DomiIRL/rgb-cube/models/tests/standoff_test_preview.png

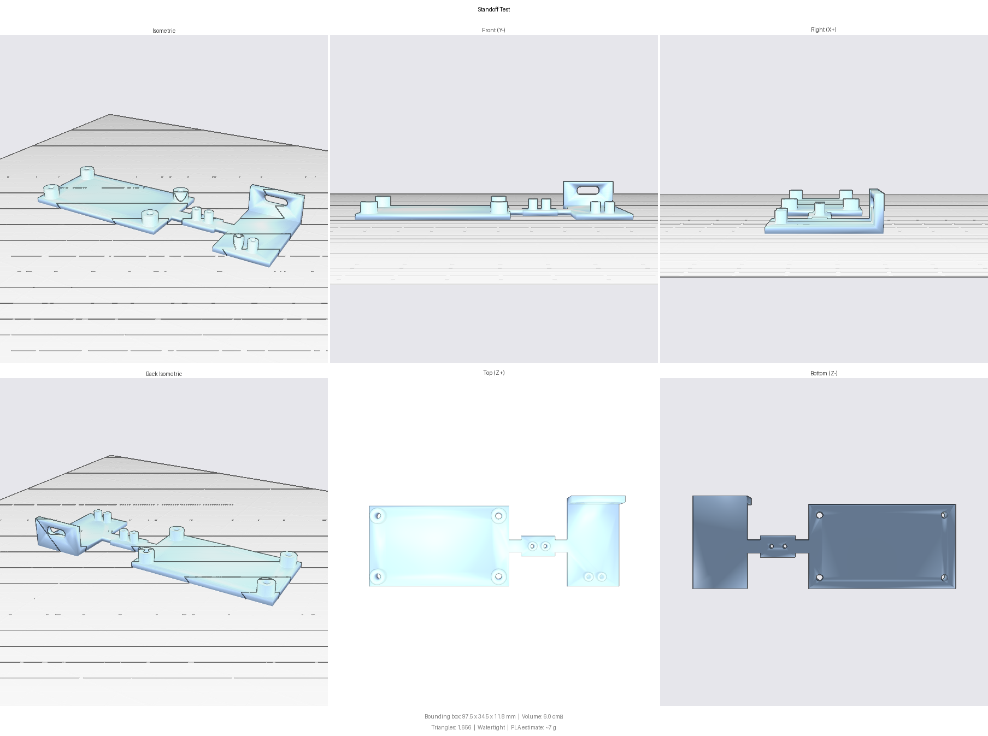
models/tests/standoff_test_preview.png
