DomiIRL/rgb-cube/code/src/Text.h

#pragma once
#include "Cube.h"

// Shows a short string on the cube's four vertical faces at once, using a 3x5
// font fixed one pixel up from the bottom edge, so it reads from any side. Text
// that fits is shown centred and static; longer text scrolls horizontally
// around each face. Drives itself frame by frame; report active() to know when
// the message has finished.
class TextScroll {
public:
    void start(const char* text, uint32_t now, uint32_t color);
    void update(Cube& cube, uint32_t now);
    bool active() const { return _active; }

private:
    static const uint8_t* glyphFor(char c);
    void drawFrame(Cube& cube) const;

    char _text[16] = "";
    uint32_t _color = 0;  // glyph colour for this message
    int _len = 0;
    int _scrollX = 0;     // x of the leftmost column (viewer space)
    int _pixelWidth = 0;  // total advance width of the text in pixels
    bool _static = false; // true when the text fits and is shown without scrolling
    uint32_t _lastMs = 0;
    uint32_t _endMs = 0;  // when a static (non-scrolling) label finishes
    bool _active = false;
};
